djgel/IntexEsp32/img/Boad3d.png

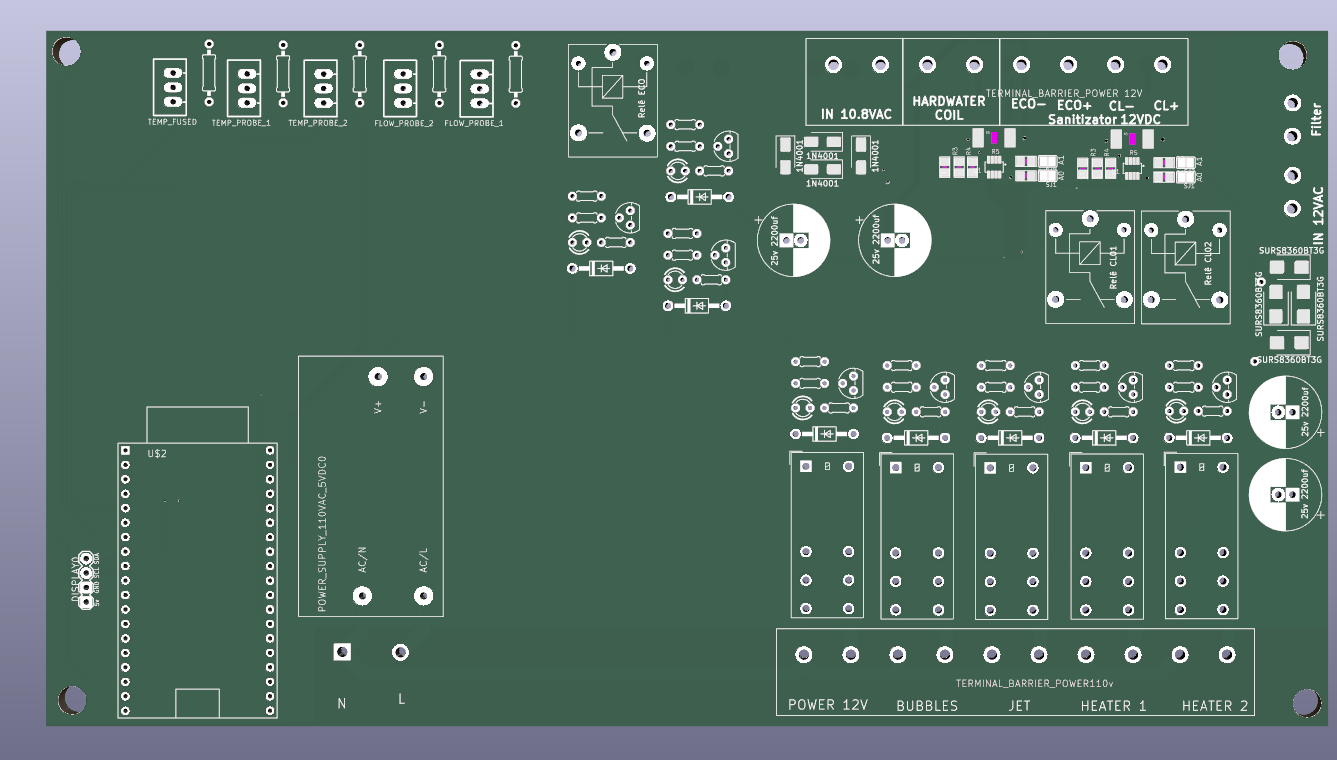
img/Boad3d.png
